tong0701/512_finalproject/Documentation/circuit/circuit_diagrams.kicad_sch

## KiCad design Documentation/circuit/circuit_diagrams.kicad_sch (2025-12-09)

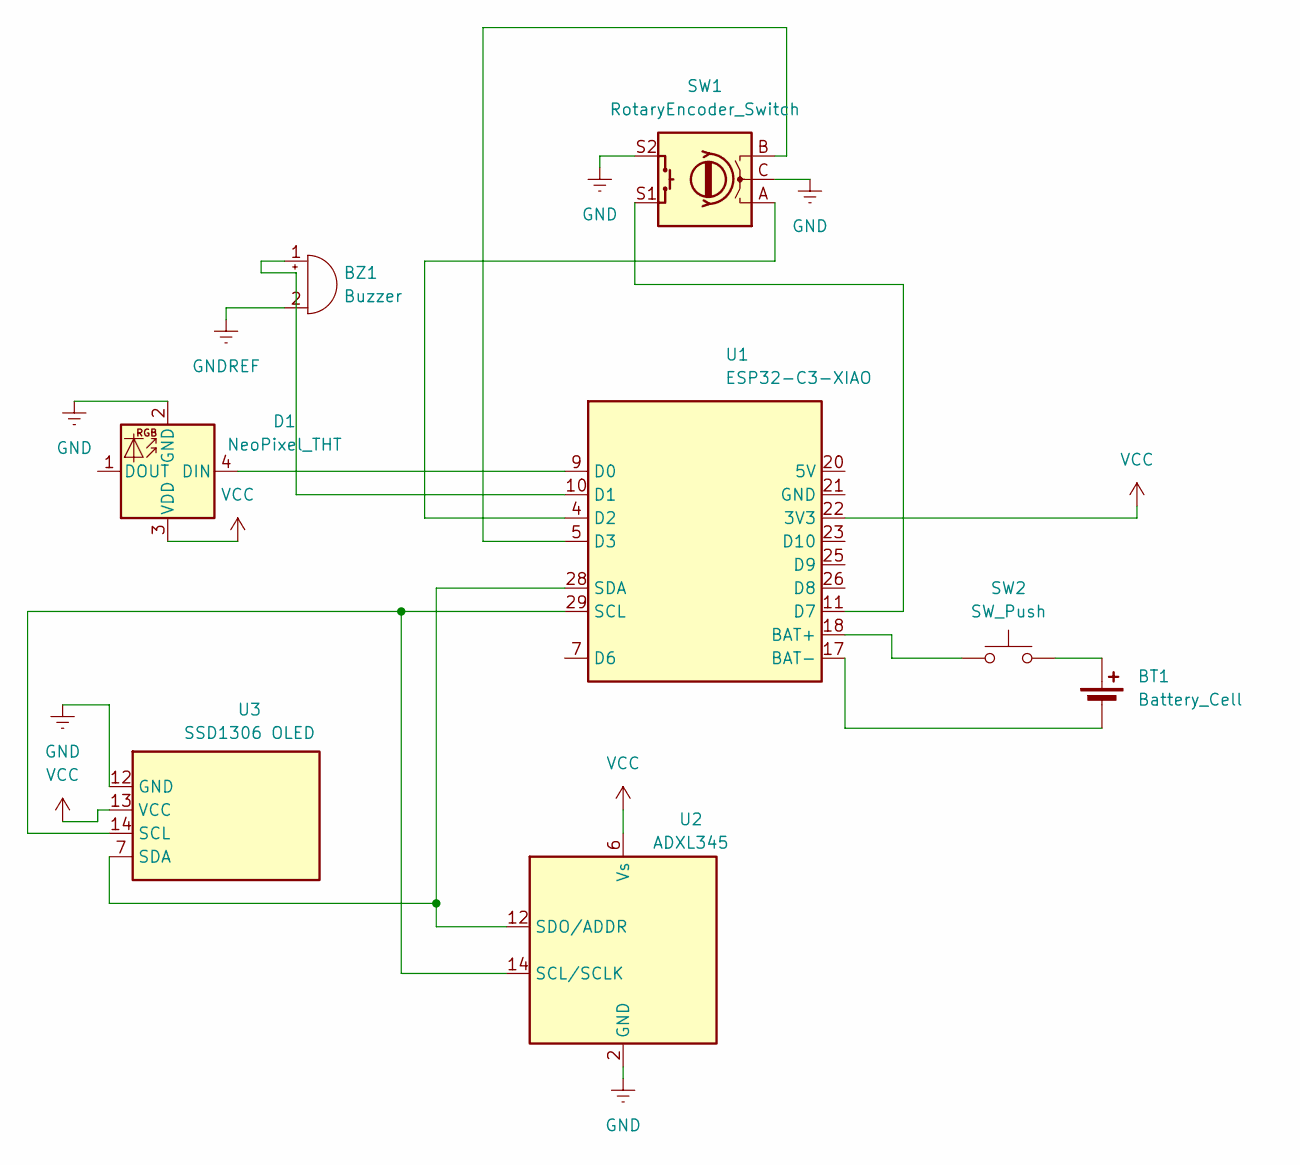
[picture p2: schematic circuit_diagrams.kicad_sch]

Parts:
BT1: Battery_Cell
BZ1: Buzzer
D1: NeoPixel_THT
SW1: RotaryEncoder_Switch
SW2: SW_Push
U1: ESP32-C3-XIAO; ESP32-C3-DevKitM-1
U2: ADXL345; LGA-14_3x5mm_P0.8mm_LayoutBorder1x6y
U3: SSD1306 OLED; LGA-14_3x5mm_P0.8mm_LayoutBorder1x6y

Connections:
GND: D1.2 (GND), SW1.C, SW1.S2, U2.2 (GND), U2.4 (GND), U2.5 (GND), U3.12 (GND)
GNDREF: BZ1.2 (-)
unnamed: BT1.1 (+), SW2.2
unnamed: BT1.2 (-), U1.17 (BAT-)
unnamed: BZ1.1 (+), U1.10 (D1)
unnamed: D1.4 (DIN), U1.9 (D0)
unnamed: SW1.A, U1.4 (D2)
unnamed: SW1.B, U1.5 (D3)
unnamed: SW1.S1, U1.11 (D7)
unnamed: SW2.1, U1.18 (BAT+)
unnamed: U1.6 (GND), U1.8 (GND), U1.12 (GND), U1.15 (GND), U1.16 (GND), U1.19 (GND), U1.24 (GND), U1.27 (GND), U1.30 (GND)
unnamed: U1.28 (SDA), U2.12 (SDO/ADDR), U3.7 (SDA)
unnamed: U1.29 (SCL), U2.14 (SCL/SCLK), U3.14 (SCL)
unnamed: U3.4 (GND), U3.5 (GND)
VCC: D1.3 (VDD), U1.22 (3V3), U2.6 (Vs), U3.13 (VCC)
